Real-time-embedded10/Magic-Music-Player/Image/Communication Flow Chart.jpg

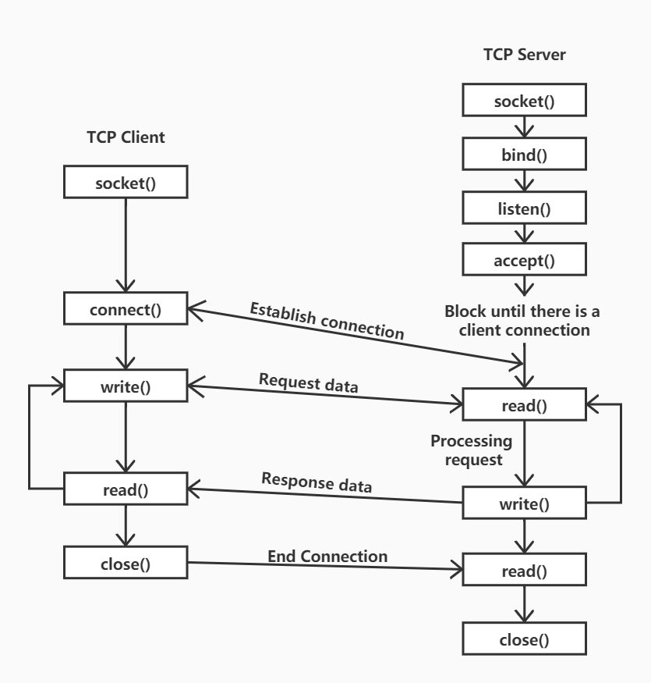
Image/Communication Flow Chart.jpg
