Real-time-embedded10/Magic-Music-Player/Image/Software.jpg

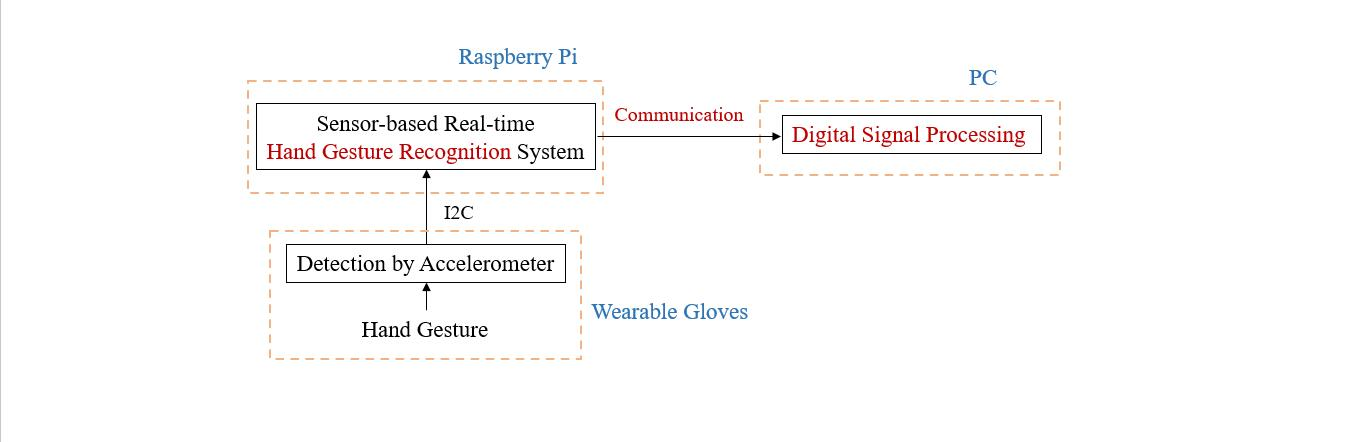
Image/Software.jpg
