Real-time-embedded10/Magic-Music-Player/Software/Hand Gesture Recognition/DATABASE/Figure/total_forward3.jpg

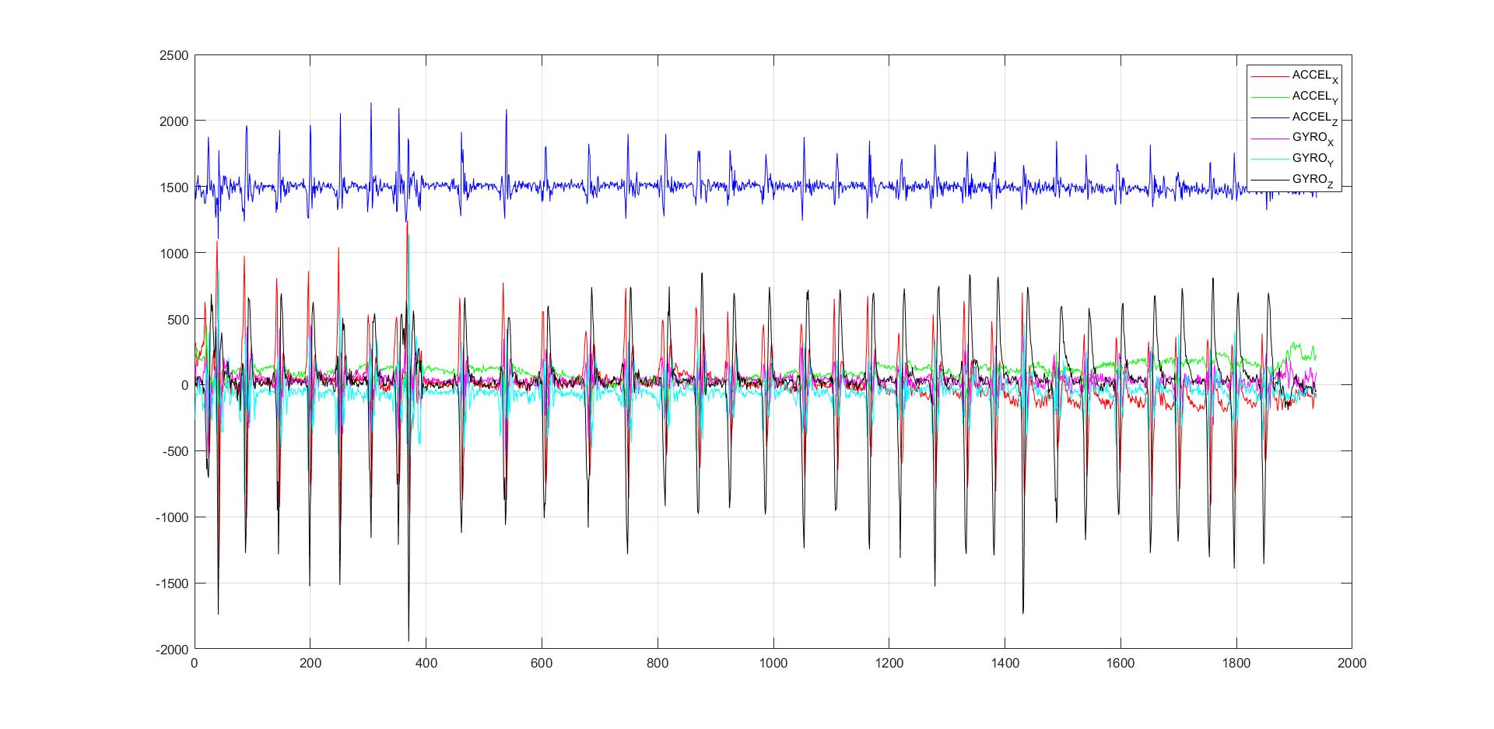
Software/Hand Gesture Recognition/DATABASE/Figure/total_forward3.jpg
