Real-time-embedded10/Magic-Music-Player/Software/Hand Gesture Recognition/DATABASE/Figure/total_right5.jpg

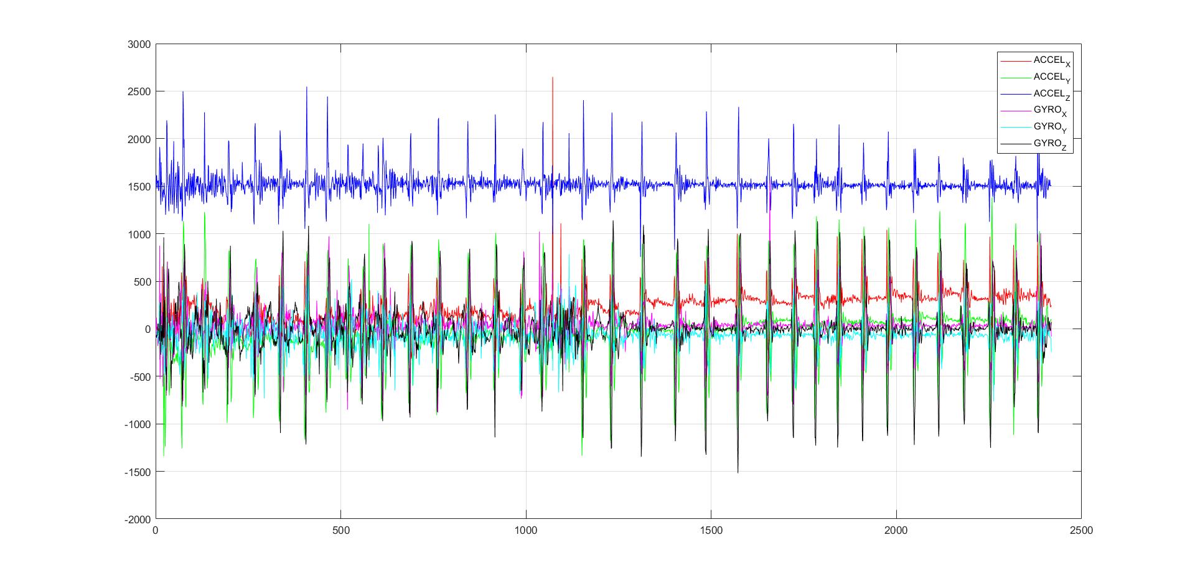
Software/Hand Gesture Recognition/DATABASE/Figure/total_right5.jpg
