Real-time-embedded10/Magic-Music-Player/Software/Hand Gesture Recognition/DATABASE/Figure/total_up1.jpg

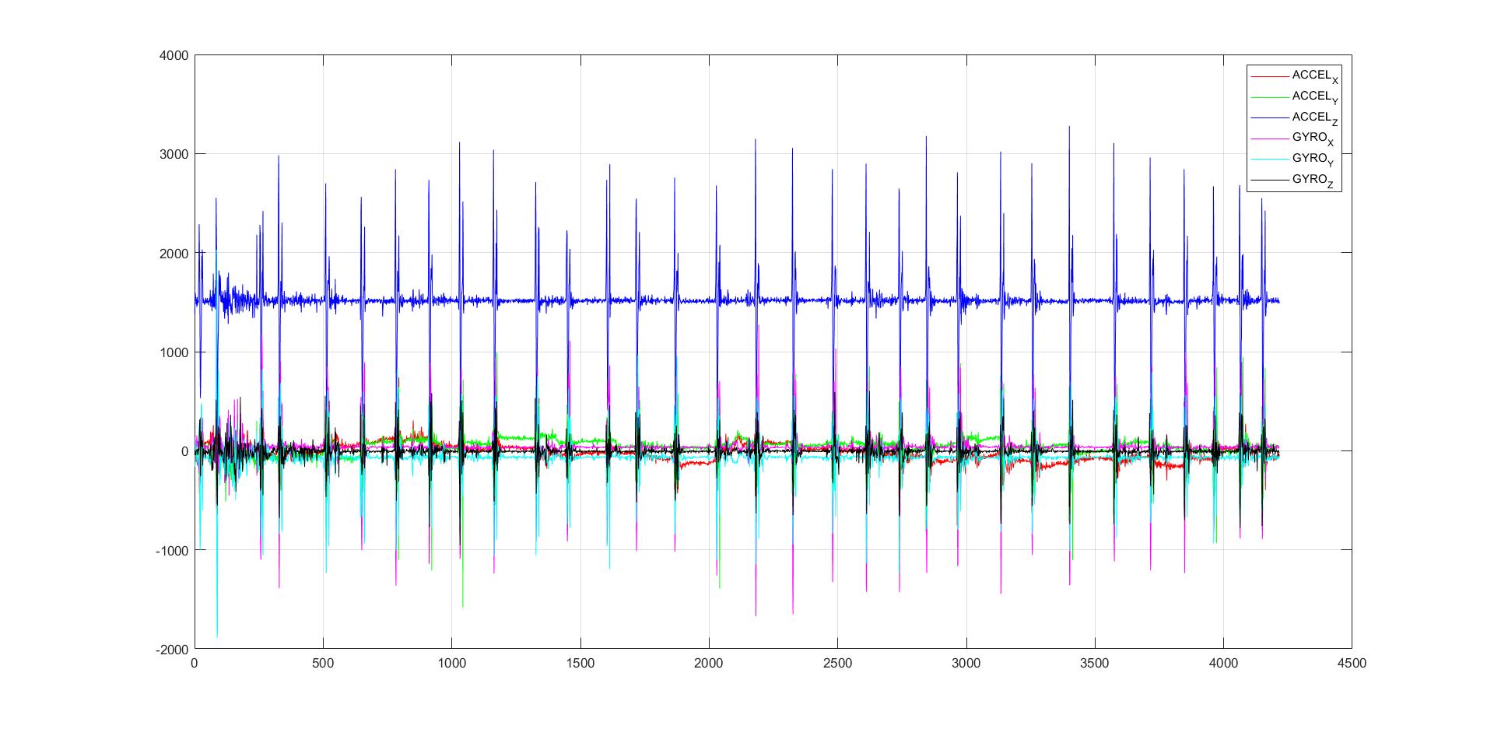
Software/Hand Gesture Recognition/DATABASE/Figure/total_up1.jpg
