Real-time-embedded10/Magic-Music-Player/Software/Hand Gesture Recognition/Software Used in Database Establishment/2. Pre-processing/Figure/detail_forward.jpg

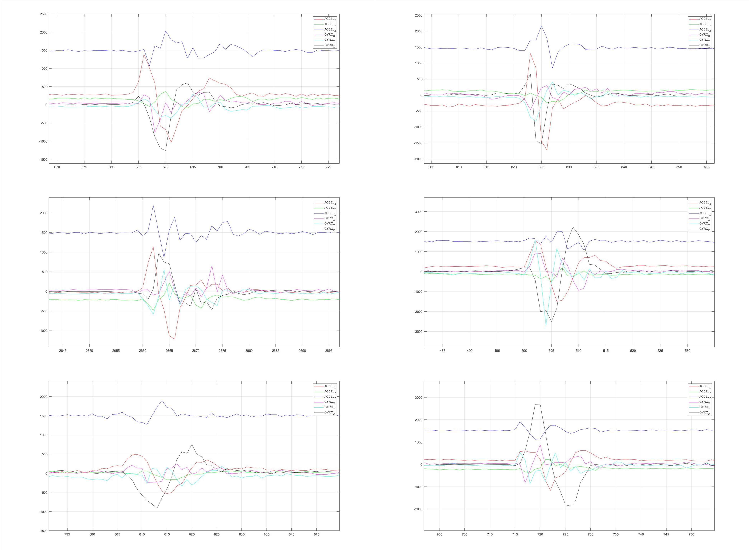
Software/Hand Gesture Recognition/Software Used in Database Establishment/2. Pre-processing/Figure/detail_forward.jpg
