Real-time-embedded10/Magic-Music-Player/Software/Hand Gesture Recognition/Software Used in Database Establishment/3. Feature Extraction/Extracted_Features.jpg

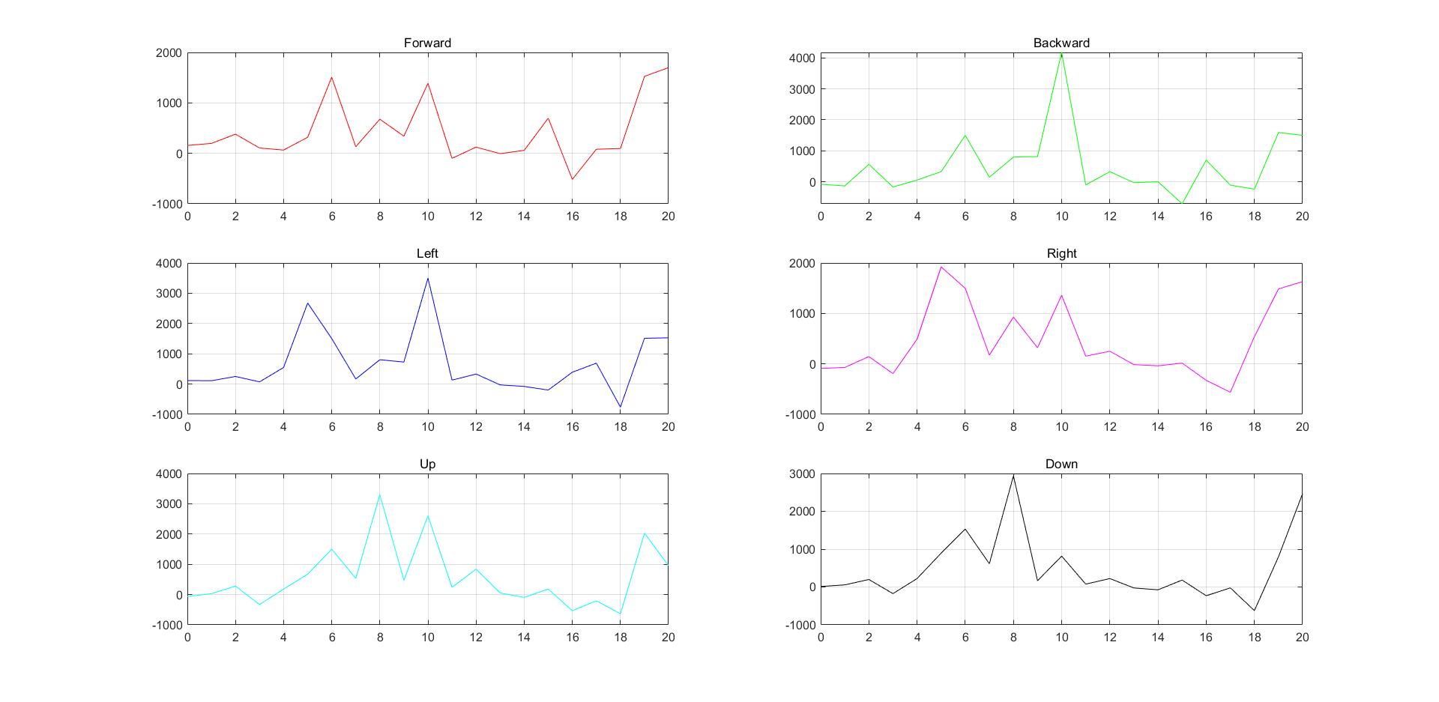
Software/Hand Gesture Recognition/Software Used in Database Establishment/3. Feature Extraction/Extracted_Features.jpg
