Real-time-embedded10/Magic-Music-Player/Software/Hand Gesture Recognition/Software Used in Database Establishment/Flowchart of Sensor-based Real-time Hand Gesture Recognition System.jpg

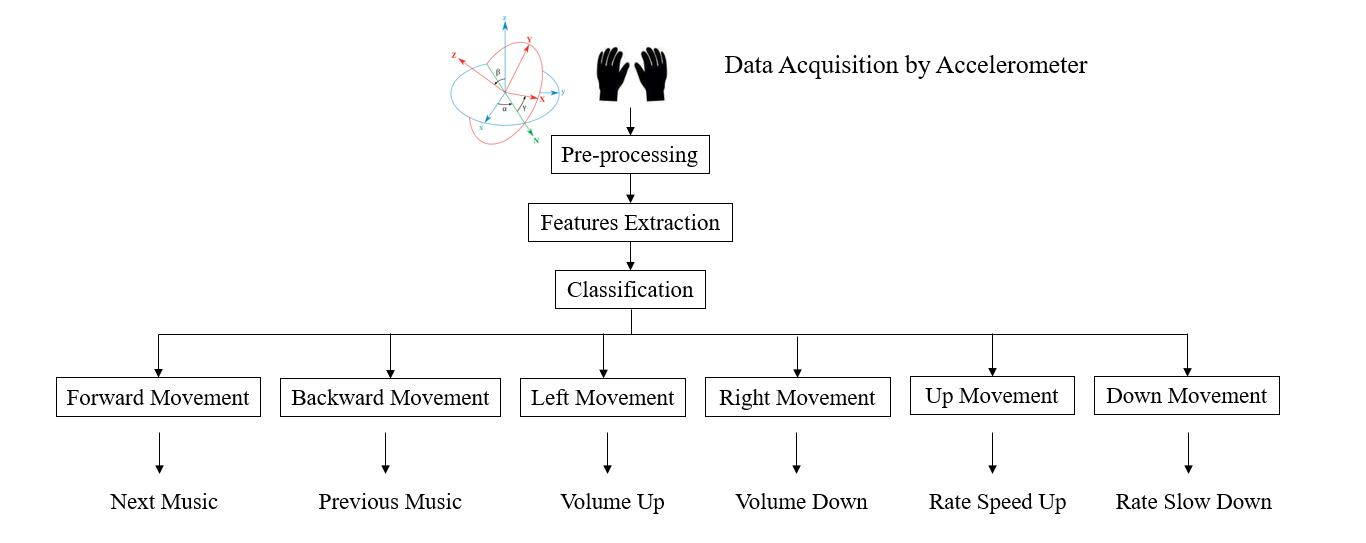
Software/Hand Gesture Recognition/Software Used in Database Establishment/Flowchart of Sensor-based Real-time Hand Gesture Recognition System.jpg
