Real-time-embedded10/Magic-Music-Player/Software/Hand Gesture Recognition/Software Used in Testing/Flowchart of Cross Validation 1.jpg

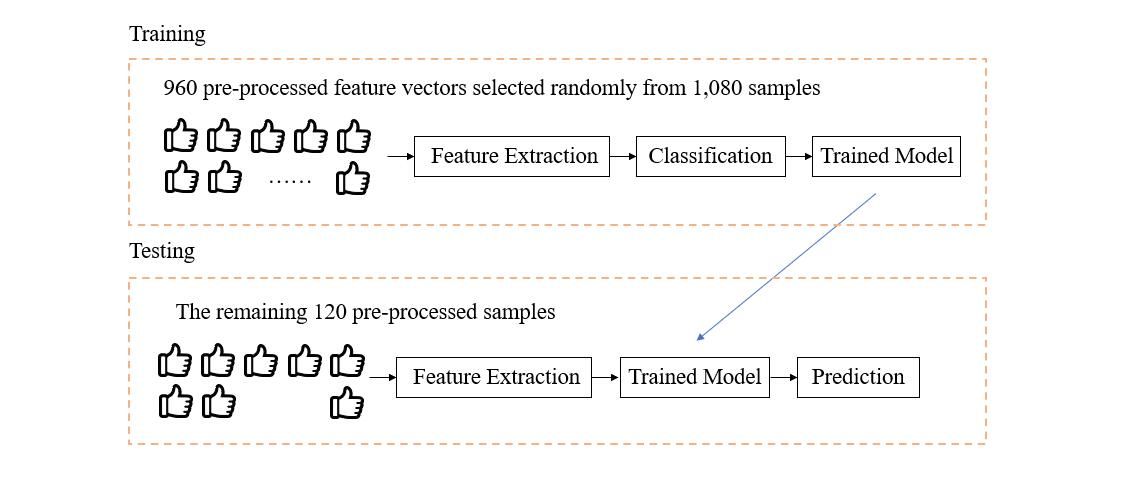
Software/Hand Gesture Recognition/Software Used in Testing/Flowchart of Cross Validation 1.jpg
