Real-time-embedded10/Magic-Music-Player/Software/Hand Gesture Recognition/Software Used in Testing/Test Result of Cross Validation 2.jpg

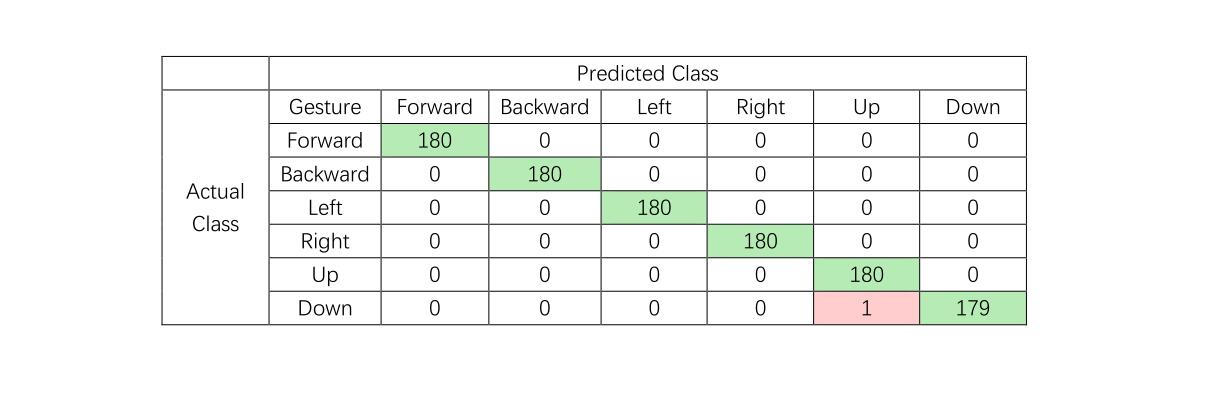
Software/Hand Gesture Recognition/Software Used in Testing/Test Result of Cross Validation 2.jpg
